skiselev/flock/images/Flock-3D_Rendering.png

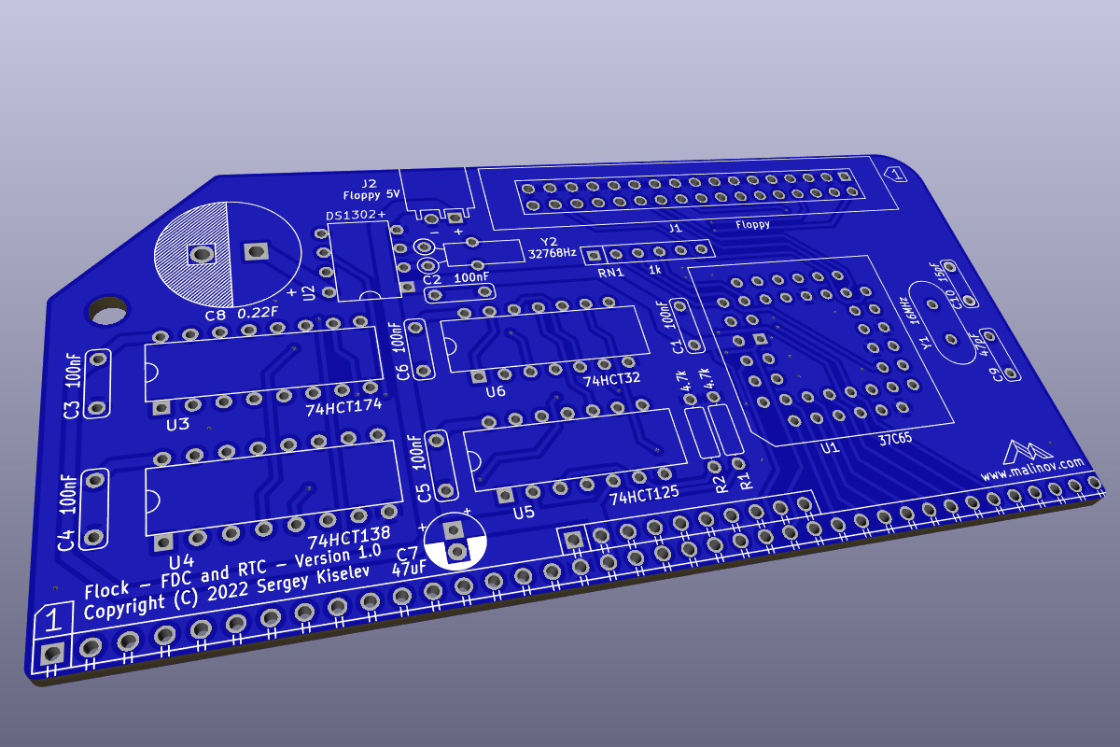
images/Flock-3D_Rendering.png
