skiselev/flock/images/Flock-PCB-Back_Side-800px.jpg

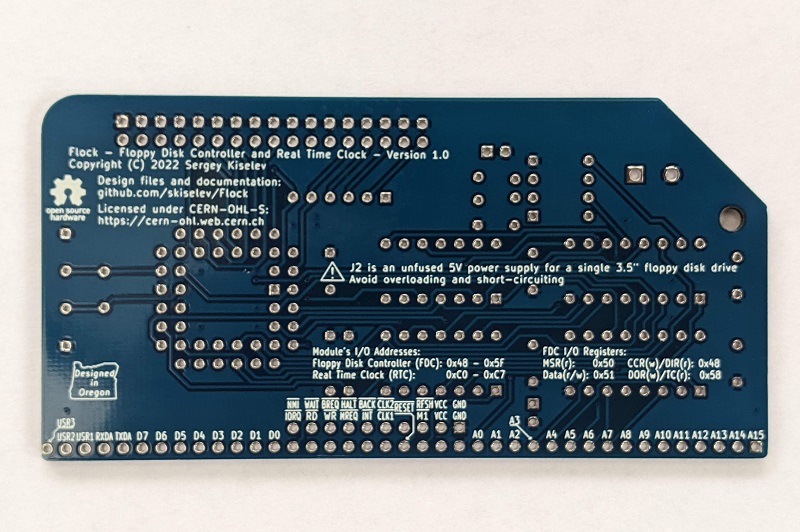
images/Flock-PCB-Back_Side-800px.jpg
