skiselev/flock/images/Flock-PCB-Front_Side-800px.jpg

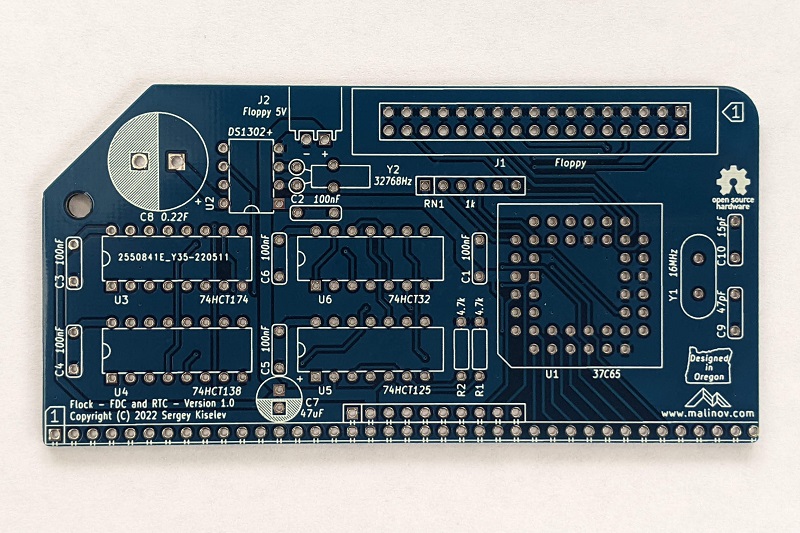
images/Flock-PCB-Front_Side-800px.jpg
